acornelissen/IDENTIDEM.design-MRF/3MF/Main Parts/door-back.3mf

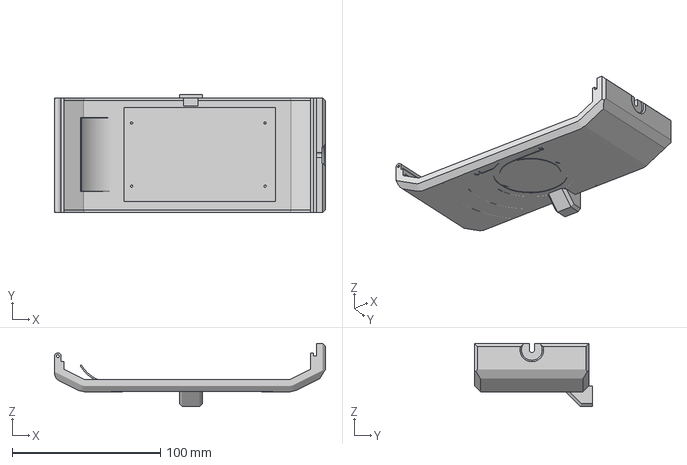
[picture p15: CAD file, 2024-06-04]
3MF/Main Parts/door-back.3mf
182.8 x 79.8 x 42.5 mm
