acornelissen/IDENTIDEM.design-MRF/3MF/Film Masks/6x7.3mf

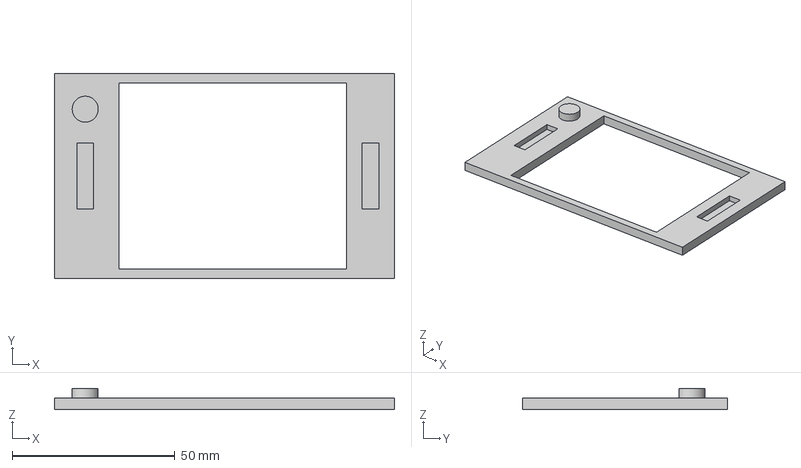
[picture p16: CAD file, 2024-05-03]
3MF/Film Masks/6x7.3mf
104.5 x 63.1 x 6.50 mm
