acornelissen/IDENTIDEM.design-MRF/3MF/Fine Parts/pressure-plate.3mf

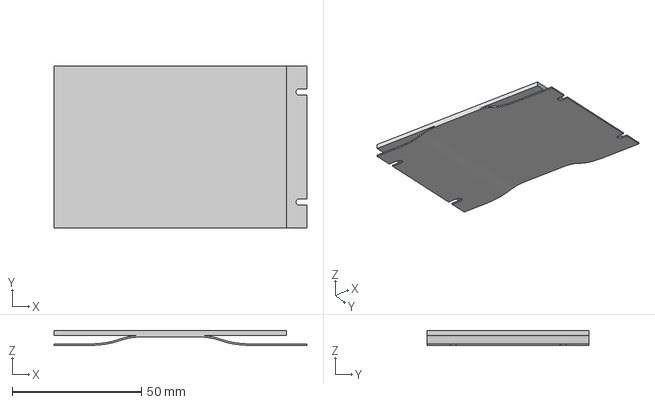
[picture p17: CAD file, 2024-05-03]
3MF/Fine Parts/pressure-plate.3mf
98.0 x 62.6 x 5.97 mm
