acornelissen/IDENTIDEM.design-MRF/3MF/Main Parts/grip.3mf

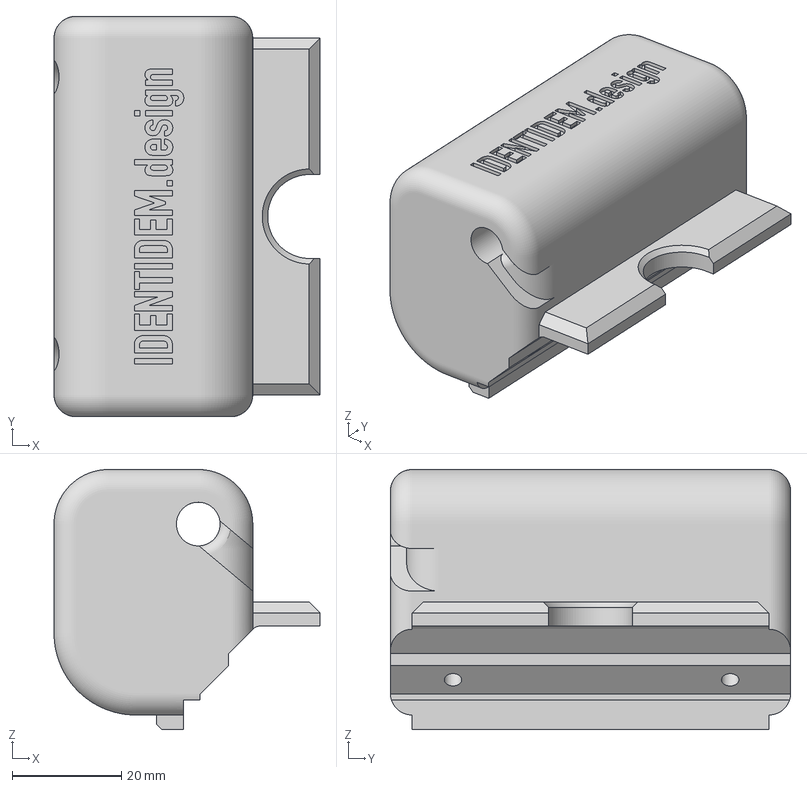
[picture p18: CAD file, 2024-05-03]
3MF/Main Parts/grip.3mf
48.7 x 73.4 x 47.7 mm
