acornelissen/IDENTIDEM.design-MRF/3MF/Fine Parts/advance-ratchet.3mf

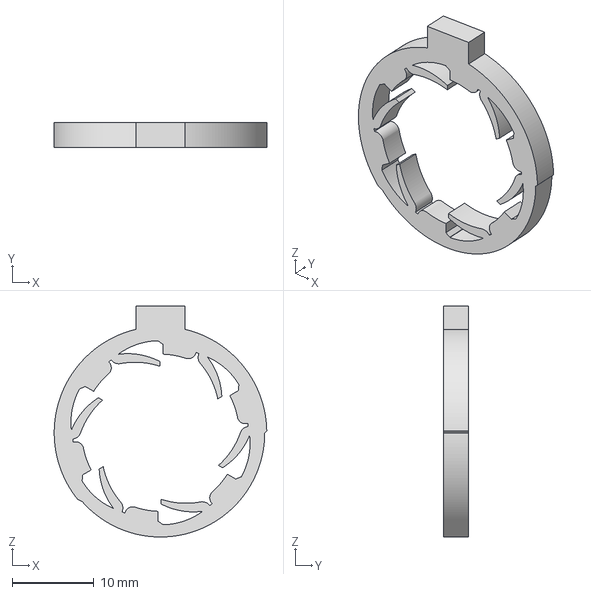
[picture p19: CAD file, 2024-05-03]
3MF/Fine Parts/advance-ratchet.3mf
26.0 x 3.00 x 28.2 mm
