acornelissen/IDENTIDEM.design-MRF/3MF/Main Parts/top-plate.3mf

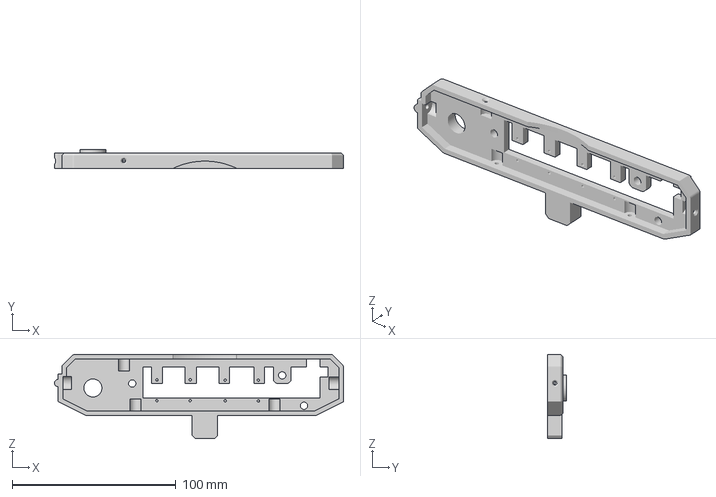
[picture p20: CAD file, 2024-05-03]
3MF/Main Parts/top-plate.3mf
176.8 x 11.4 x 51.4 mm
