acornelissen/IDENTIDEM.design-MRF/3MF/Fine Parts/advance-post.3mf

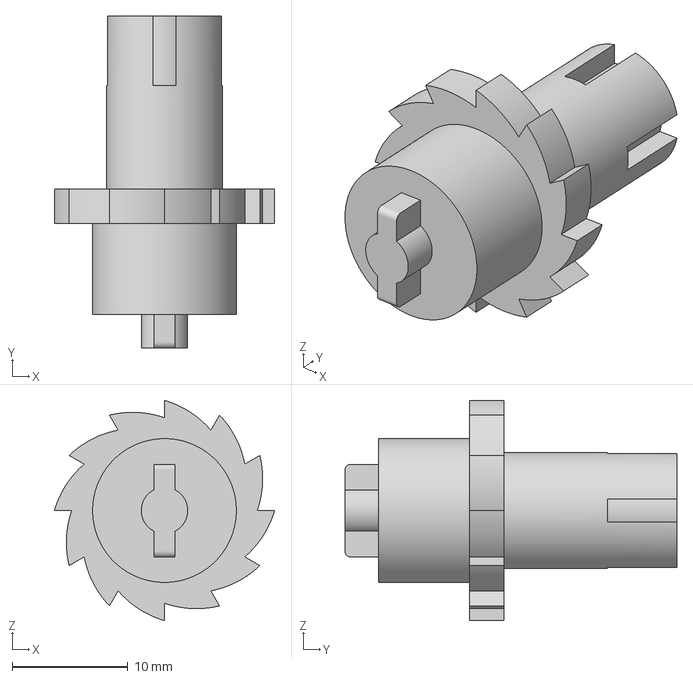
[picture p21: CAD file, 2024-05-03]
3MF/Fine Parts/advance-post.3mf
19.0 x 28.6 x 19.0 mm
