acornelissen/IDENTIDEM.design-MRF/3MF/Main Parts/advance-knob.3mf

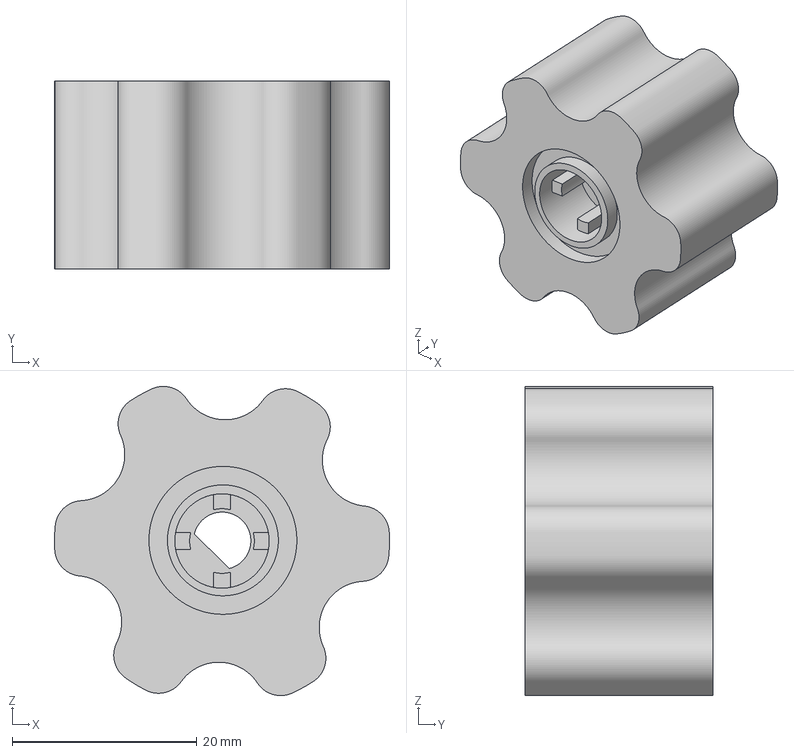
[picture p22: CAD file, 2024-05-03]
3MF/Main Parts/advance-knob.3mf
36.2 x 20.3 x 33.4 mm
