acornelissen/IDENTIDEM.design-MRF/3MF/Fine Parts/left (from back) spool.3mf

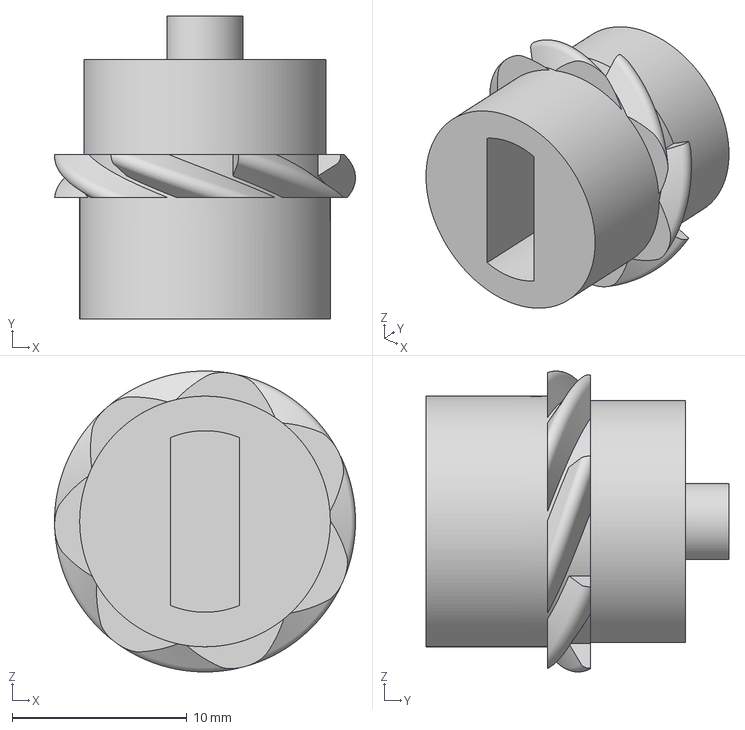
[picture p23: CAD file, 2024-05-03]
3MF/Fine Parts/left (from back) spool.3mf
17.2 x 17.3 x 17.2 mm
