acornelissen/IDENTIDEM.design-MRF/3MF/Main Parts/body-bottom.3mf

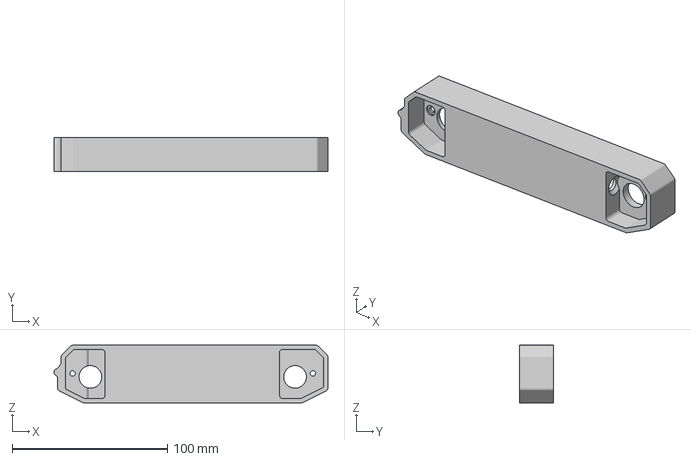
[picture p24: CAD file, 2024-05-03]
3MF/Main Parts/body-bottom.3mf
176.7 x 22.0 x 37.2 mm
