acornelissen/IDENTIDEM.design-MRF/3MF/Fine Parts/right (from back) spool.3mf

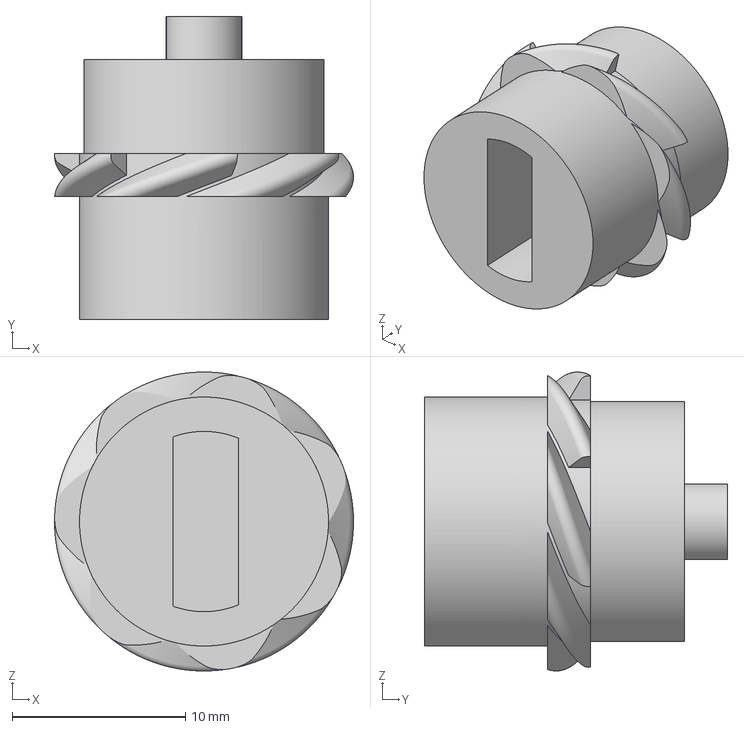
[picture p25: CAD file, 2024-05-03]
3MF/Fine Parts/right (from back) spool.3mf
17.2 x 17.5 x 17.2 mm
