acornelissen/IDENTIDEM.design-MRF/3MF/Fine Parts/spool-key (optional).3mf

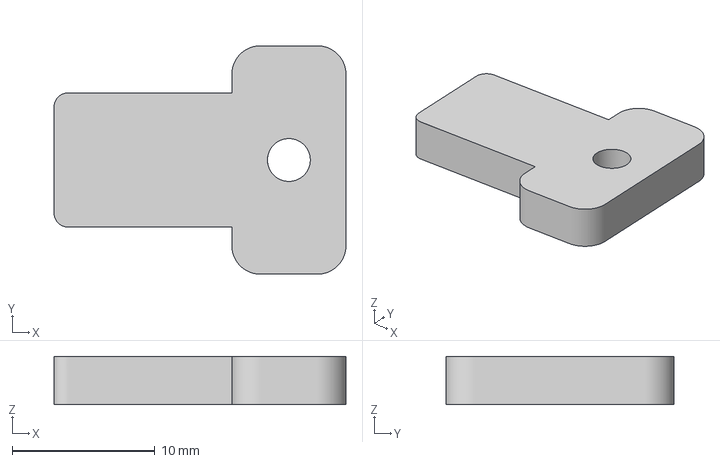
[picture p26: CAD file, 2024-05-03]
3MF/Fine Parts/spool-key (optional).3mf
20.5 x 16.0 x 3.38 mm
