acornelissen/IDENTIDEM.design-MRF/Firmware/src/hardware.cpp

#include "hardware.h"

// For constants used in initializers like SCREEN_WIDTH, SS_NEOPIX, etc.
#include "mrfconstants.h"
#include <Wire.h> // For display constructors if they take &Wire

// Hardware init
// ---------------------
// Inputs
Adafruit_seesaw encoder;
Adafruit_ADS1115 ads1015;
Adafruit_MPU6050 mpu; 

seesaw_NeoPixel sspixel = seesaw_NeoPixel(1, SS_NEOPIX, NEO_GRB + NEO_KHZ800);
Bounce2::Button lbutton = Bounce2::Button();
Bounce2::Button rbutton = Bounce2::Button();

// Battery gauge
Adafruit_MAX17048 maxlipo;

// Lightmeter
BH1750 lightMeter;

// LiDAR setup
TFMPlus tfminiplus;
HardwareSerial lidarSerial(2); // Using serial port 2

// Display setup
Adafruit_SH1107 display(SCREEN_WIDTH, SCREEN_HEIGHT, &Wire, OLED_RESET, 1000000, 1000000);
Adafruit_SSD1306 display_ext(SCREEN_WIDTH, SCREEN_HEIGHT_EXT, &Wire, OLED_RESET);
U8G2_FOR_ADAFRUIT_GFX u8g2;
U8G2_FOR_ADAFRUIT_GFX u8g2_ext;
// ---------------------
