acornelissen/IDENTIDEM.design-MRF/Firmware/include/cyclefuncs.h

#ifndef CYCLEFUNCS_H_
#define CYCLEFUNCS_H_

#include <Arduino.h> // For String type used in function signature

// Functions to cycle values
// ---------------------
void cycleApertures(String direction);
void cycleISOs();
void cycleLenses();
void cycleCalibLenses();
void cycleFormats();
// ---------------------

#endif // CYCLEFUNCS_H_
