acornelissen/IDENTIDEM.design-MRF/Firmware/include/interface.h

#ifndef INTERFACE_H_
#define INTERFACE_H_

// Functions to draw UI
// ---------------------
void drawMainUI();
void drawConfigUI();
void drawCalibUI();
void drawExternalUI();
void drawSleepUI();
// ---------------------

#endif // INTERFACE_H_
