acornelissen/IDENTIDEM.design-MRF/Firmware/src/lenses.cpp

#include "lenses.h"
#include <Arduino.h> // For String type if used in initialization (not directly here but good practice for String members)

// Lens and film format definitions
Lens lenses[] = {
    {5063, "50/6.3", {0, 0, 0, 0, 0, 0, 0}, {1, 1.2, 1.5, 2, 3, 5, 10}, {0, 6.3, 8, 11, 16, 22, 32, 0, 0}, {0, 17, 128, 109}, false},
    {6563, "65/6.3", {330, 312, 299, 287, 276, 268, 261}, {1, 1.2, 1.5, 2, 3, 5, 10}, {0, 6.3, 8, 11, 16, 22, 32, 0, 0}, {0, 17, 128, 109}, true},
    {7556, "75/5.6", {0, 0, 0, 0, 0, 0, 0}, {1, 1.2, 1.5, 2, 3, 5, 10}, {0, 5.6, 8, 11, 16, 22, 32, 45, 0}, {9, 24, 110, 95}, false},
    {9035, "90/3.5", {0, 0, 0, 0, 0, 0, 0}, {1, 1.2, 1.5, 2, 3, 5, 10}, {3.5, 4, 5.6, 8, 11, 16, 22, 32, 0}, {18, 32, 92, 79}, false},
    {10035, "100/3.5", {0, 0, 0, 0, 0, 0, 0}, {1, 1.2, 1.5, 2, 3, 5, 10}, {3.5, 4, 5.6, 8, 11, 16, 22, 32, 0}, {23, 36, 84, 71}, false},
    {10028, "100/2.8", {0, 0, 0, 0, 0, 0, 0}, {1, 1.2, 1.5, 2, 3, 5, 10}, {2.8, 4, 5.6, 8, 11, 16, 22, 32, 0}, {23, 36, 84, 71}, false},
    {12747, "127/4.7", {0, 0, 0, 0, 0, 0, 0}, {1, 1.2, 1.5, 2, 3, 5, 10}, {4.7, 5.6, 8, 11, 16, 22, 32, 45, 64}, {31, 43, 66, 57}, false},
    {15056, "150/5.6", {0, 0, 0, 0, 0, 0, 0}, {1, 1.2, 1.5, 2, 3, 5, 10}, {5.6, 8, 11, 16, 22, 32, 45, 0, 0}, {36, 48, 56, 47}, false},
    {25005, "250/5.0", {0, 0, 0, 0, 0, 0, 0}, {1, 1.2, 1.5, 2, 3, 5, 10}, {5, 8, 11, 16, 22, 32, 45, 0, 0}, {47, 57, 34, 29}, false}
};

const int LENSES_SIZE = sizeof(lenses) / sizeof(lenses[0]);
