acornelissen/IDENTIDEM.design-MRF/Firmware/src/mrfconstants.cpp

#include "mrfconstants.h"

const int ISOS[] = {50, 80, 100, 125, 200, 400, 500, 640, 800, 1600, 3200, 6400};
const int ISOS_SIZE = sizeof(ISOS) / sizeof(ISOS[0]);

const float CALIB_DISTANCES[] = {1, 1.2, 1.5, 2, 3, 5, 10};
const int CALIB_DISTANCES_SIZE = sizeof(CALIB_DISTANCES) / sizeof(CALIB_DISTANCES[0]);
